fabiobaltieri/avr-micro-usb/firmware-nikon-remote/requests.h

#define CUSTOM_RQ_SHOOT         0
#define CUSTOM_RQ_SHOOT_SILENT  1
#define CUSTOM_RQ_IR_ON         2
#define CUSTOM_RQ_R_ON          3
#define CUSTOM_RQ_R_BLINK       4
#define CUSTOM_RQ_OFF           5

#define CUSTOM_RQ_RESET         0xff
